aeonSolutions/AeonLabs-HomeAutomation-Power-Managment-Single-SolarCELL-18650-battery-storage/Circuit Schematic/image_2023-06-02_174031338.png

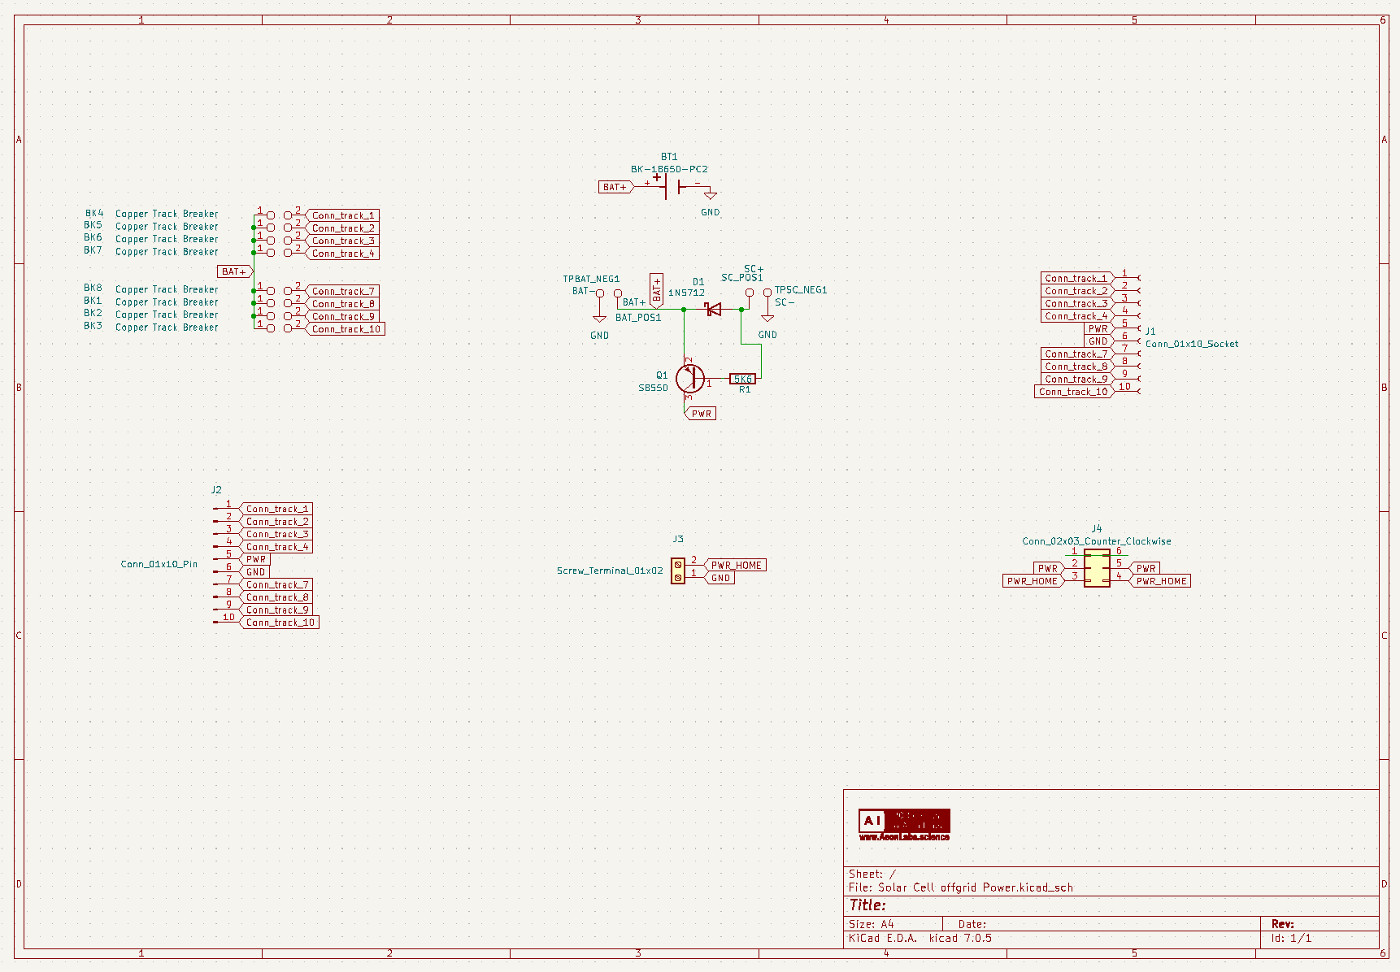
Circuit Schematic/image_2023-06-02_174031338.png
